scott-cjx/explorekb-75/hardware/keyboard-pcb/explorekb75-rev4/explorekb-rev4.kicad_sch

## KiCad design hardware/keyboard-pcb/explorekb75-rev4/explorekb-rev4.kicad_sch (2023-09-29)

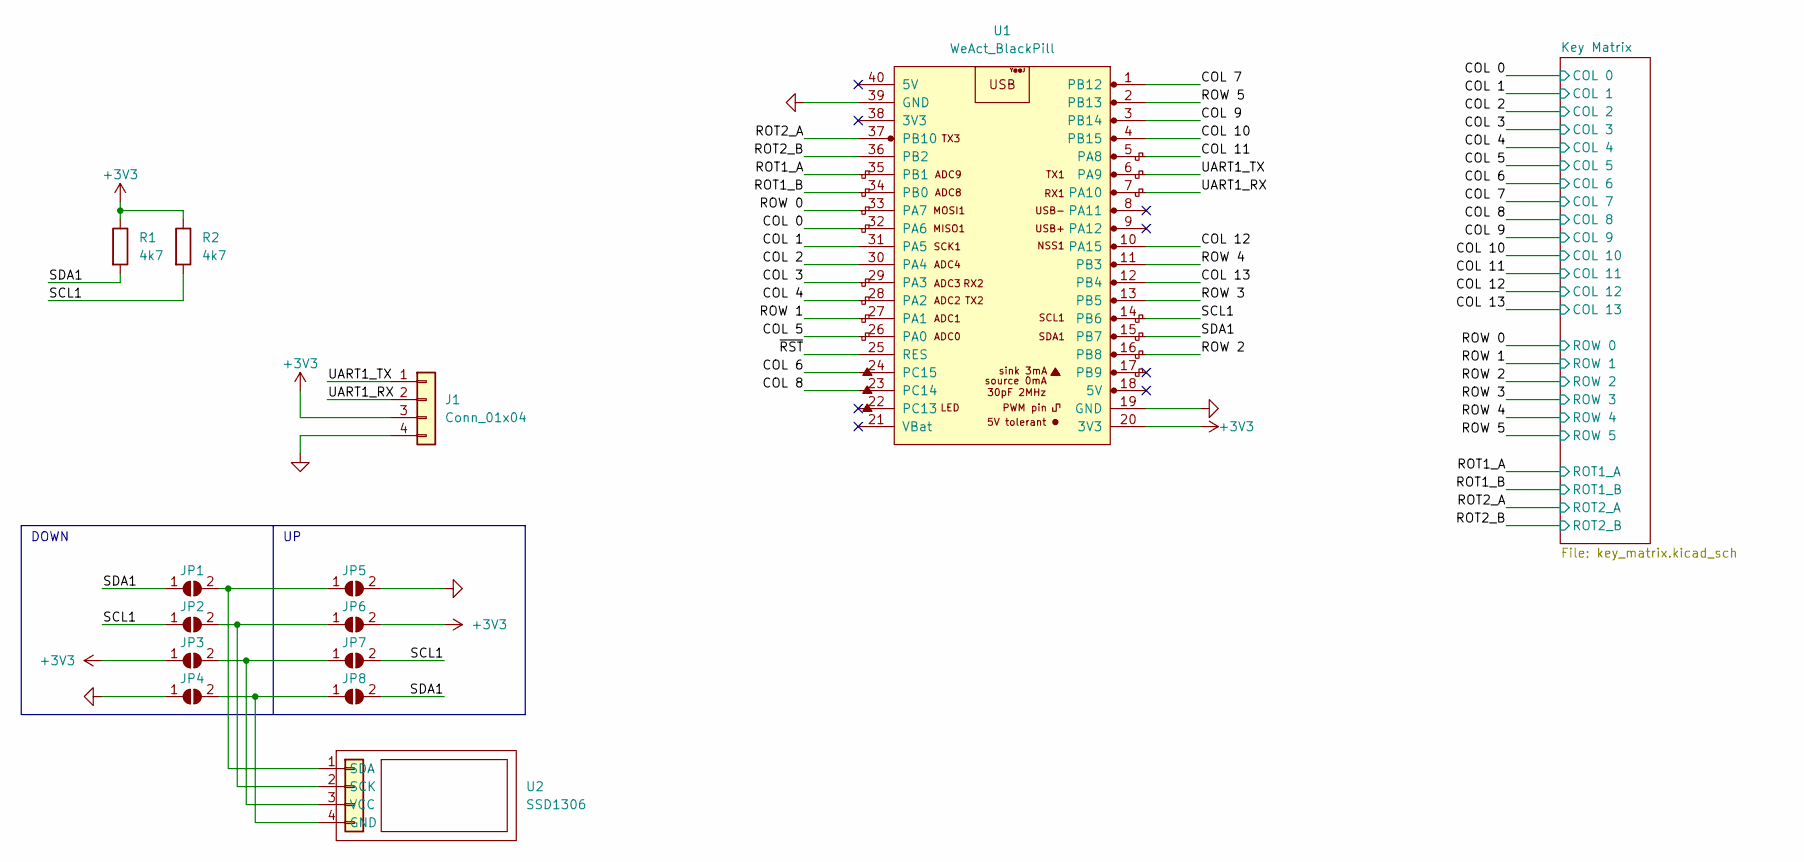
[picture p15: schematic explorekb-rev4.kicad_sch]

Parts:
J1: Conn_01x04
JP1, JP2, JP3, JP4, JP5, JP6, JP7, JP8: SolderJumper_2_Open; SolderJumper-2_P1.3mm_Open_RoundedPad1.0x1.5mm
R1, R2: 4k7; C_0603
U1: WeAct_BlackPill; WeAct_BlackPill_2
U2: SSD1306; SSD1306_128X32

Connections:
+3V3: J1.3, JP3.1 (A), JP6.2 (B), R1.1, R2.1, U1.20 (3V3)
COL 0: U1.32 (PA6)
COL 1: U1.31 (PA5)
COL 2: U1.30 (PA4)
COL 3: U1.29 (PA3)
COL 4: U1.28 (PA2)
COL 5: U1.26 (PA0)
COL 6: U1.24 (PC15)
COL 7: U1.1 (PB12)
COL 8: U1.23 (PC14)
COL 9: U1.3 (PB14)
COL 10: U1.4 (PB15)
COL 11: U1.5 (PA8)
COL 12: U1.10 (PA15)
COL 13: U1.12 (PB4)
GND: J1.4, JP4.1 (A), JP5.2 (B), U1.19 (GND), U1.39 (GND)
unnamed: JP1.2 (B), JP5.1 (A), U2.1 (SDA)
unnamed: JP2.2 (B), JP6.1 (A), U2.2 (SCK)
unnamed: JP3.2 (B), JP7.1 (A), U2.3 (VCC)
unnamed: JP4.2 (B), JP8.1 (A), U2.4 (GND)
ROT1_A: U1.35 (PB1)
ROT1_B: U1.34 (PB0)
ROT2_A: U1.37 (PB10)
ROT2_B: U1.36 (PB2)
ROW 0: U1.33 (PA7)
ROW 1: U1.27 (PA1)
ROW 2: U1.16 (PB8)
ROW 3: U1.13 (PB5)
ROW 4: U1.11 (PB3)
ROW 5: U1.2 (PB13)
SCL1: JP2.1 (A), JP7.2 (B), R2.2, U1.14 (PB6)
SDA1: JP1.1 (A), JP8.2 (B), R1.2, U1.15 (PB7)
UART1_RX: J1.2, U1.7 (PA10)
UART1_TX: J1.1, U1.6 (PA9)
~RST: U1.25 (RES)

Notes on the sheet:
DOWN
