scott-cjx/explorekb-75/hardware/keyboard-pcb/explorekb75-rev4/key_matrix.kicad_sch

## KiCad design hardware/keyboard-pcb/explorekb75-rev4/key_matrix.kicad_sch (2023-09-29)

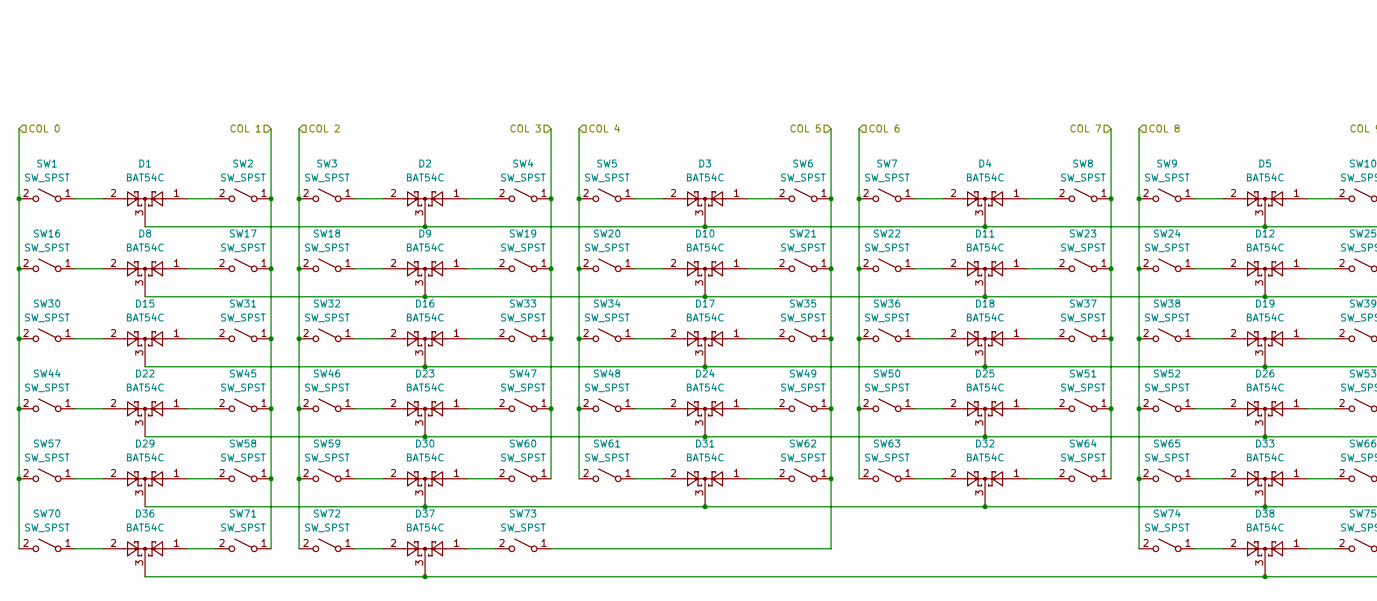
[picture p16: schematic key_matrix.kicad_sch, part in row 1, column 1]

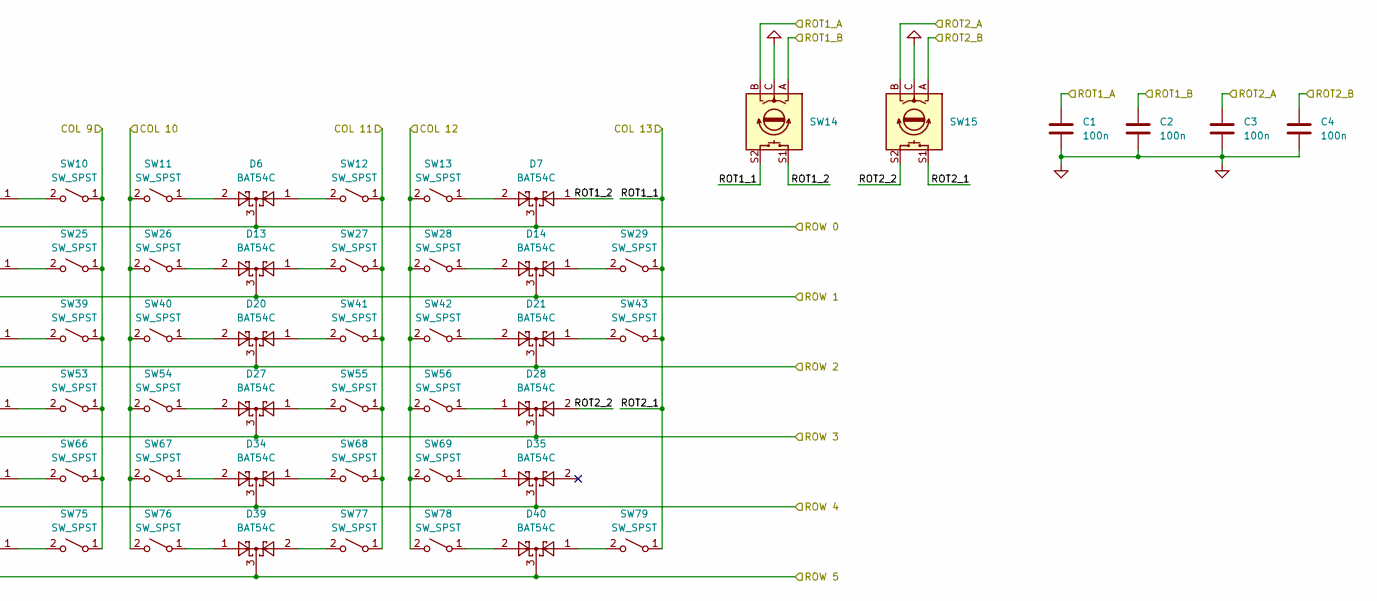
[picture p17: schematic key_matrix.kicad_sch, part in row 1, column 2]

Parts:
C1, C2, C3, C4: 100n; C_0603
D1, D2, D3, D4, D5, D6, D7, D8, D9, D10, D11, D12, D13, D14, D15, D16, D17, D18, D19, D20, D21, D22, D23, D24, D25, D26, D27, D28, D29, D30, D31, D32, D33, D34, D35, D36, D37, D38, D39, D40: BAT54C; SOT-23
SW1, SW2, SW3, SW4, SW5, SW6, SW7, SW8, SW9, SW10, SW11, SW12, SW13, SW16, SW17, SW18, SW19, SW20, SW21, SW22, SW23, SW24, SW25, SW26, SW27, SW28, SW29, SW30, SW31, SW32, SW33, SW34, SW35, SW36, SW37, SW38, SW39, SW40, SW41, SW42, SW43, SW44, SW45, SW46, SW47, SW48, SW49, SW50, SW51, SW52, SW53, SW54, SW55, SW56, SW57, SW58, SW59, SW60, SW61, SW62, SW63, SW64, SW65, SW66, SW67, SW68, SW69, SW70, SW71, SW72, SW73, SW74, SW75, SW76, SW77, SW78, SW79: SW_SPST; MX_HS_Optional
SW14, SW15: RotaryEncoder_Switch; RotaryEncoder_EC11_MX_Opt

Connections:
COL 0: SW1.2 (B), SW16.2 (B), SW30.2 (B), SW44.2 (B), SW57.2 (B), SW70.2 (B)
COL 1: SW2.1 (A), SW17.1 (A), SW31.1 (A), SW45.1 (A), SW58.1 (A), SW71.1 (A)
COL 2: SW3.2 (B), SW18.2 (B), SW32.2 (B), SW46.2 (B), SW59.2 (B), SW72.2 (B)
COL 3: SW4.1 (A), SW19.1 (A), SW33.1 (A), SW47.1 (A), SW60.1 (A)
COL 4: SW5.2 (B), SW20.2 (B), SW34.2 (B), SW48.2 (B), SW61.2 (B)
COL 5: SW6.1 (A), SW21.1 (A), SW35.1 (A), SW49.1 (A), SW62.1 (A), SW73.1 (A)
COL 6: SW7.2 (B), SW22.2 (B), SW36.2 (B), SW50.2 (B), SW63.2 (B)
COL 7: SW8.1 (A), SW23.1 (A), SW37.1 (A), SW51.1 (A), SW64.1 (A)
COL 8: SW9.2 (B), SW24.2 (B), SW38.2 (B), SW52.2 (B), SW65.2 (B), SW74.2 (B)
COL 9: SW10.1 (A), SW25.1 (A), SW39.1 (A), SW53.1 (A), SW66.1 (A), SW75.1 (A)
COL 10: SW11.2 (B), SW26.2 (B), SW40.2 (B), SW54.2 (B), SW67.2 (B), SW76.2 (B)
COL 11: SW12.1 (A), SW27.1 (A), SW41.1 (A), SW55.1 (A), SW68.1 (A), SW77.1 (A)
COL 12: SW13.2 (B), SW28.2 (B), SW42.2 (B), SW56.2 (B), SW69.2 (B), SW78.2 (B)
COL 13: SW14.S2, SW15.S1, SW29.1 (A), SW43.1 (A), SW79.1 (A)
GND: C1.2, C2.2, C3.2, C4.2, SW14.C, SW15.C
unnamed: D1.1, SW2.2 (B)
unnamed: D1.2, SW1.1 (A)
unnamed: D2.1, SW4.2 (B)
unnamed: D2.2, SW3.1 (A)
unnamed: D3.1, SW6.2 (B)
unnamed: D3.2, SW5.1 (A)
unnamed: D4.1, SW8.2 (B)
unnamed: D4.2, SW7.1 (A)
unnamed: D5.1, SW10.2 (B)
unnamed: D5.2, SW9.1 (A)
unnamed: D6.1, SW12.2 (B)
unnamed: D6.2, SW11.1 (A)
unnamed: D7.2, SW13.1 (A)
unnamed: D8.1, SW17.2 (B)
unnamed: D8.2, SW16.1 (A)
unnamed: D9.1, SW19.2 (B)
unnamed: D9.2, SW18.1 (A)
unnamed: D10.1, SW21.2 (B)
unnamed: D10.2, SW20.1 (A)
unnamed: D11.1, SW23.2 (B)
unnamed: D11.2, SW22.1 (A)
unnamed: D12.1, SW25.2 (B)
unnamed: D12.2, SW24.1 (A)
unnamed: D13.1, SW27.2 (B)
unnamed: D13.2, SW26.1 (A)
unnamed: D14.1, SW29.2 (B)
unnamed: D14.2, SW28.1 (A)
unnamed: D15.1, SW31.2 (B)
unnamed: D15.2, SW30.1 (A)
unnamed: D16.1, SW33.2 (B)
unnamed: D16.2, SW32.1 (A)
unnamed: D17.1, SW35.2 (B)
unnamed: D17.2, SW34.1 (A)
unnamed: D18.1, SW37.2 (B)
unnamed: D18.2, SW36.1 (A)
unnamed: D19.1, SW39.2 (B)
unnamed: D19.2, SW38.1 (A)
unnamed: D20.1, SW41.2 (B)
unnamed: D20.2, SW40.1 (A)
unnamed: D21.1, SW43.2 (B)
unnamed: D21.2, SW42.1 (A)
unnamed: D22.1, SW45.2 (B)
unnamed: D22.2, SW44.1 (A)
unnamed: D23.1, SW47.2 (B)
unnamed: D23.2, SW46.1 (A)
unnamed: D24.1, SW49.2 (B)
unnamed: D24.2, SW48.1 (A)
unnamed: D25.1, SW51.2 (B)
unnamed: D25.2, SW50.1 (A)
unnamed: D26.1, SW53.2 (B)
unnamed: D26.2, SW52.1 (A)
unnamed: D27.1, SW55.2 (B)
unnamed: D27.2, SW54.1 (A)
unnamed: D28.1, SW56.1 (A)
unnamed: D29.1, SW58.2 (B)
unnamed: D29.2, SW57.1 (A)
unnamed: D30.1, SW60.2 (B)
unnamed: D30.2, SW59.1 (A)
unnamed: D31.1, SW62.2 (B)
unnamed: D31.2, SW61.1 (A)
unnamed: D32.1, SW64.2 (B)
unnamed: D32.2, SW63.1 (A)
unnamed: D33.1, SW66.2 (B)
unnamed: D33.2, SW65.1 (A)
unnamed: D34.1, SW68.2 (B)
unnamed: D34.2, SW67.1 (A)
unnamed: D35.1, SW69.1 (A)
unnamed: D36.1, SW71.2 (B)
unnamed: D36.2, SW70.1 (A)
unnamed: D37.1, SW73.2 (B)
unnamed: D37.2, SW72.1 (A)
unnamed: D38.1, SW75.2 (B)
unnamed: D38.2, SW74.1 (A)
unnamed: D39.1, SW76.1 (A)
unnamed: D39.2, SW77.2 (B)
unnamed: D40.1, SW79.2 (B)
unnamed: D40.2, SW78.1 (A)
ROT1_2: D7.1, SW14.S1
ROT1_A: C1.1, SW14.B
ROT1_B: C2.1, SW14.A
ROT2_2: D28.2, SW15.S2
ROT2_A: C3.1, SW15.B
ROT2_B: C4.1, SW15.A
ROW 0: D1.3, D2.3, D3.3, D4.3, D5.3, D6.3, D7.3
ROW 1: D8.3, D9.3, D10.3, D11.3, D12.3, D13.3, D14.3
ROW 2: D15.3, D16.3, D17.3, D18.3, D19.3, D20.3, D21.3
ROW 3: D22.3, D23.3, D24.3, D25.3, D26.3, D27.3, D28.3
ROW 4: D29.3, D30.3, D31.3, D32.3, D33.3, D34.3, D35.3
ROW 5: D36.3, D37.3, D38.3, D39.3, D40.3
